wanghao666123/dummy_study/esp32-iot/firmware/examples/device-dashboard/screenshots/dashboard.webp

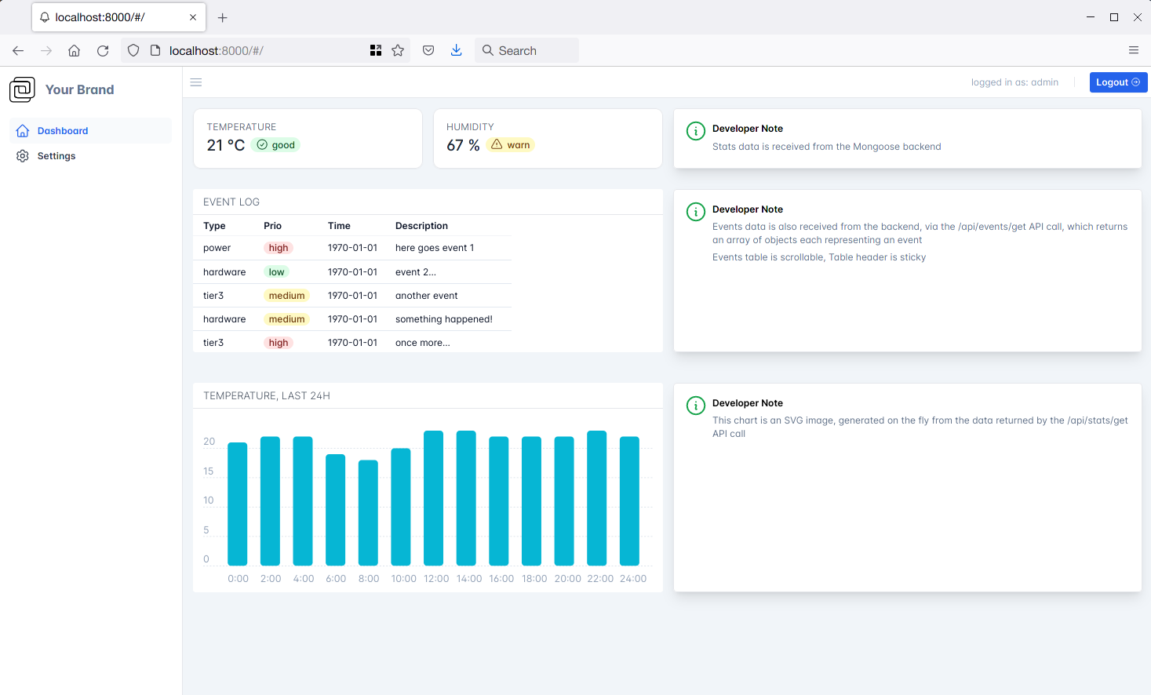
esp32-iot/firmware/examples/device-dashboard/screenshots/dashboard.webp
