wanghao666123/dummy_study/esp32-iot/firmware/examples/device-dashboard/screenshots/login.webp

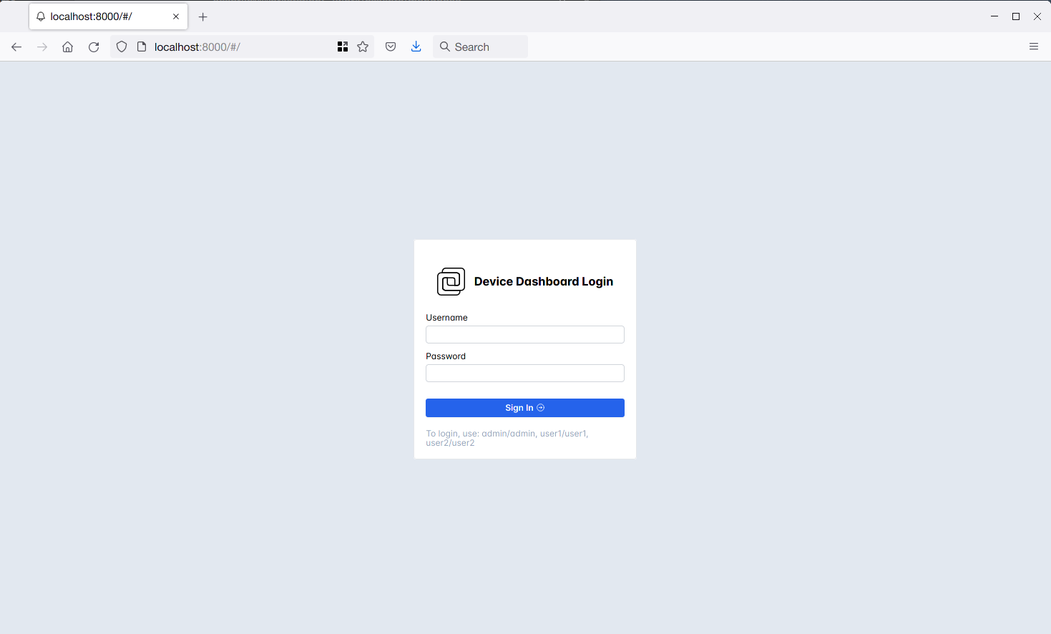
esp32-iot/firmware/examples/device-dashboard/screenshots/login.webp
