wanghao666123/dummy_study/esp32-iot/firmware/examples/uart-bridge/screenshots/dashboard.png

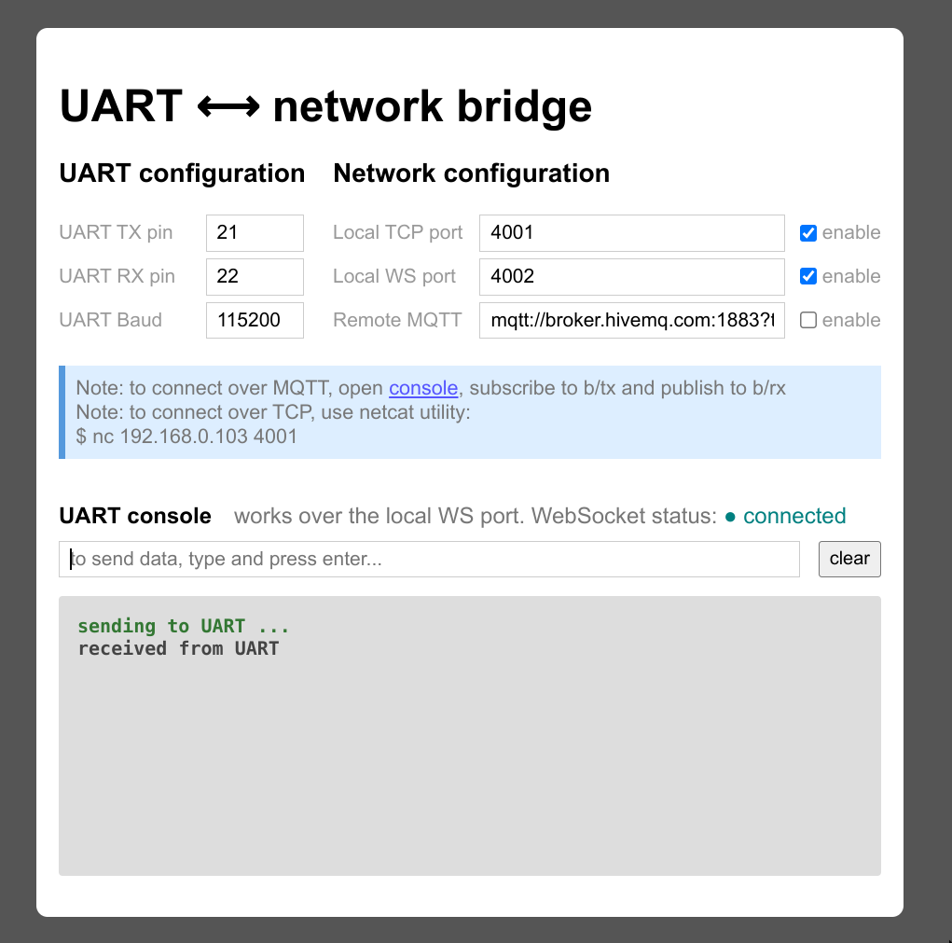
esp32-iot/firmware/examples/uart-bridge/screenshots/dashboard.png
