wanghao666123/dummy_study/esp32-iot/firmware/examples/video-stream/images/5.jpg

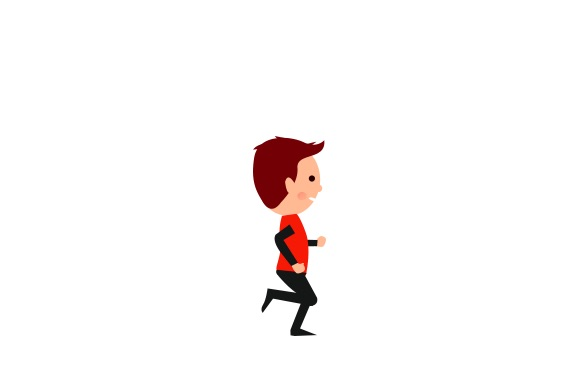
esp32-iot/firmware/examples/video-stream/images/5.jpg
