wanghao666123/dummy_study/esp32-iot/firmware/examples/webui-login/web_root/user.png

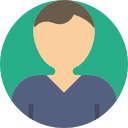
esp32-iot/firmware/examples/webui-login/web_root/user.png
