wanghao666123/dummy_study/harmonic_reducer/mini8_parameters.JPG

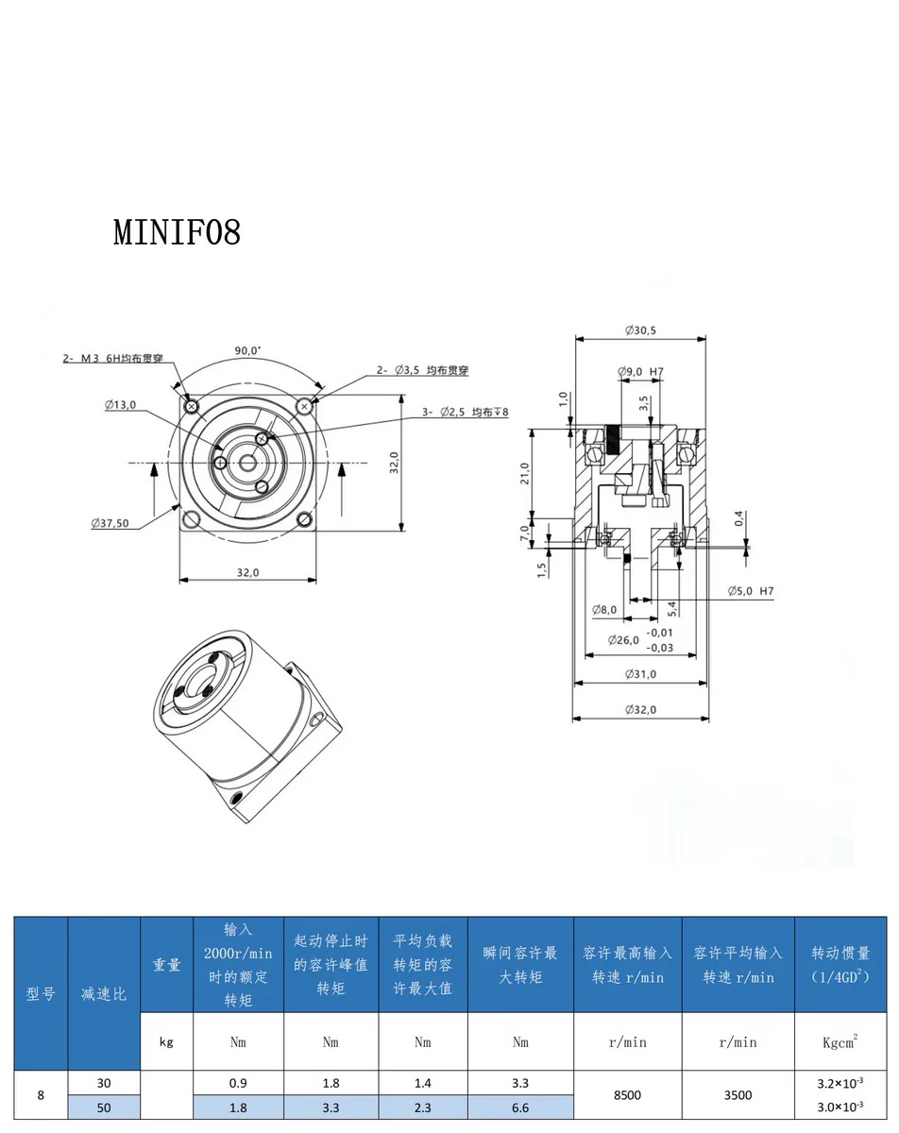
harmonic_reducer/mini8_parameters.JPG
