wanghao666123/dummy_study/harmonic_reducer/mini11_parameters.JPG

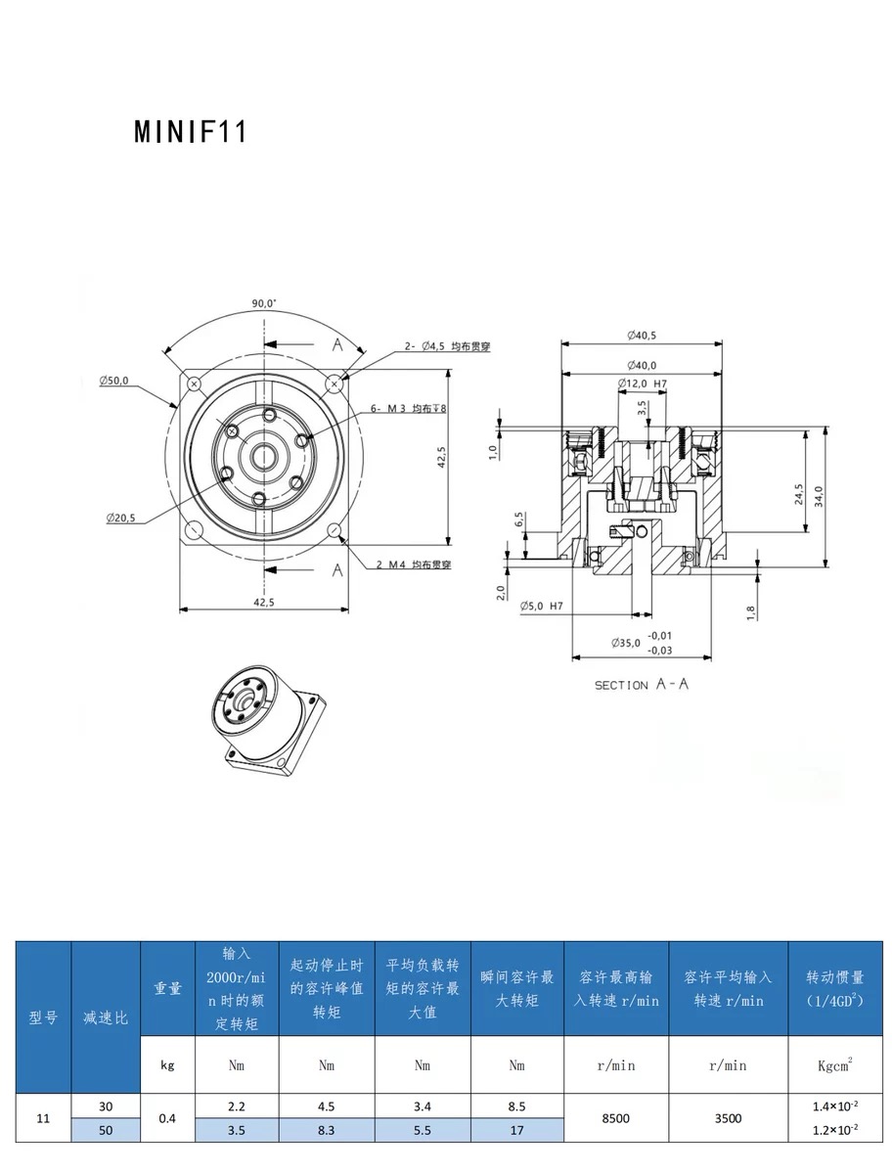
harmonic_reducer/mini11_parameters.JPG
