wanghao666123/dummy_study/ros2/dummy_ws/src/dummy-ros2_description/meshes/link2_1_1.stl

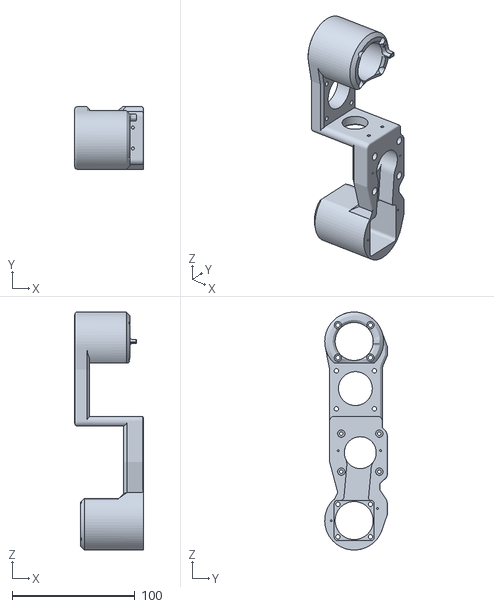
[picture p33: CAD file, 2024-07-29]
ros2/dummy_ws/src/dummy-ros2_description/meshes/link2_1_1.stl
55.8 x 51.0 x 194.0
