wanghao666123/dummy_study/ros2/dummy_ws/src/dummy-ros2_description/meshes/link3_1_1.stl

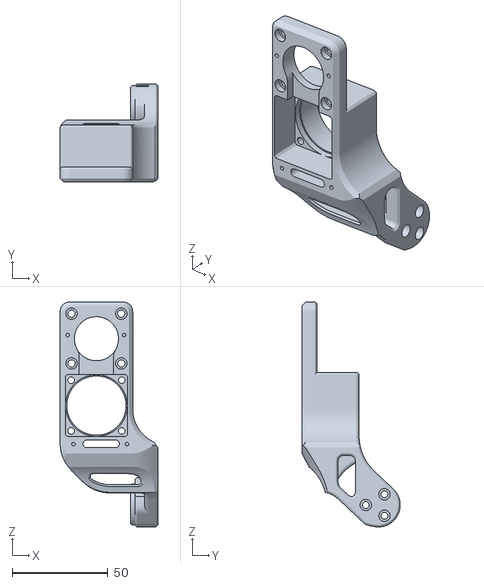
[picture p34: CAD file, 2024-07-29]
ros2/dummy_ws/src/dummy-ros2_description/meshes/link3_1_1.stl
51.1 x 51.5 x 117.7
