wanghao666123/dummy_study/ros2/dummy_ws/src/dummy-ros2_description/meshes/link5_1_1.stl

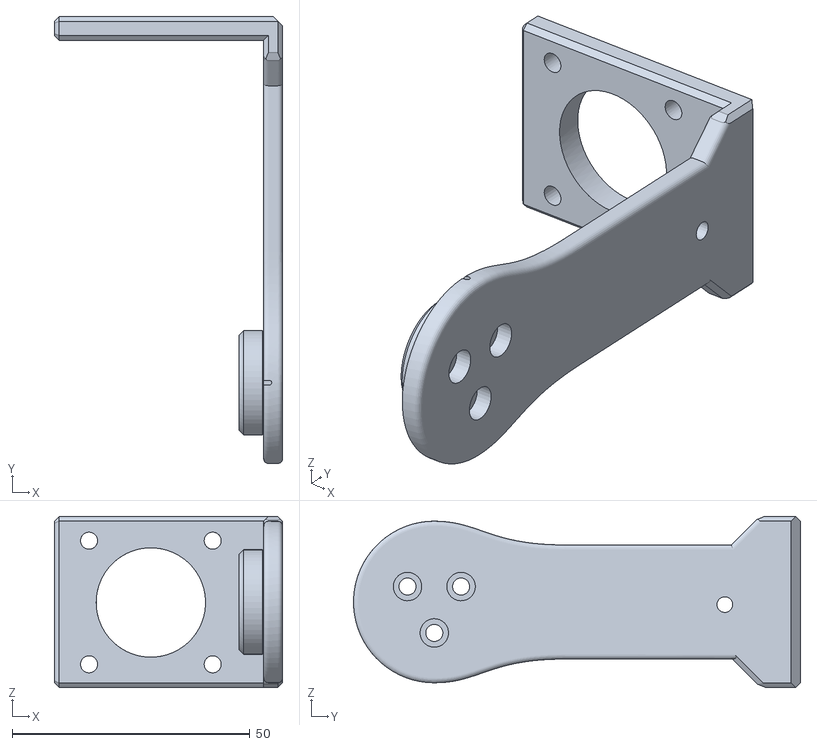
[picture p35: CAD file, 2024-07-29]
ros2/dummy_ws/src/dummy-ros2_description/meshes/link5_1_1.stl
48.0 x 94.0 x 36.0
