wanghao666123/dummy_study/3d-model/joint6.stl

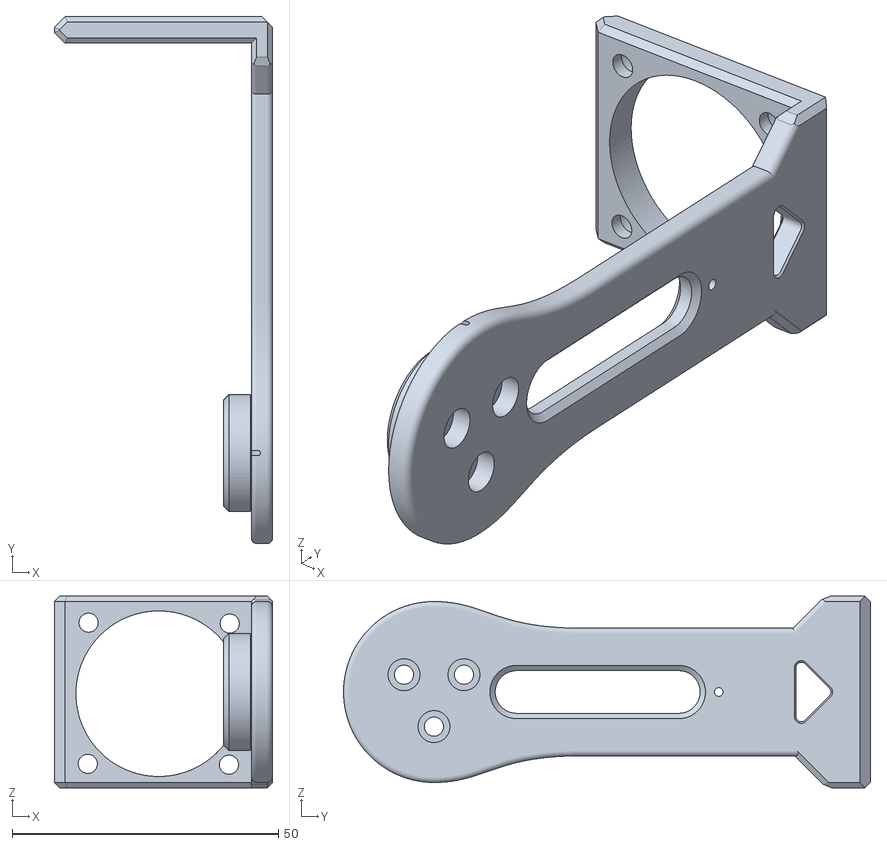
[picture p36: CAD file, 2023-11-14]
3d-model/joint6.stl
41.0 x 99.0 x 36.0
