wanghao666123/dummy_study/3d-model/latest/j4.stl

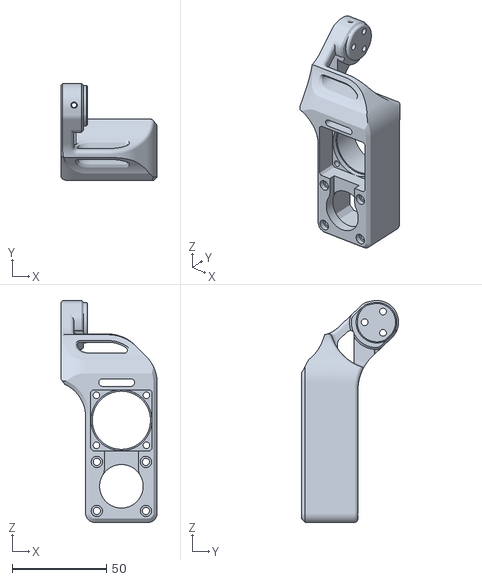
[picture p37: CAD file, 2023-12-19]
3d-model/latest/j4.stl
51.1 x 51.5 x 117.7
