wanghao666123/dummy_study/ros2/dummy_ws/src/dummy-ros2_description/meshes/base_link.stl

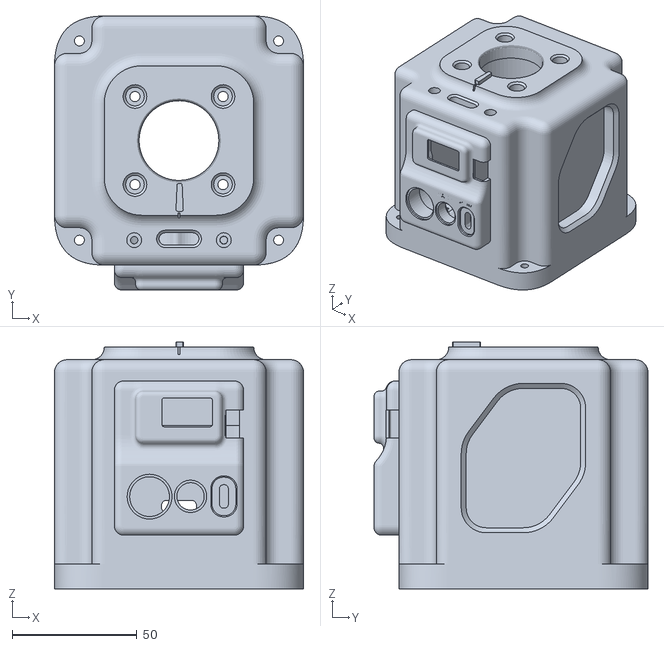
[picture p38: CAD file, 2024-07-29]
ros2/dummy_ws/src/dummy-ros2_description/meshes/base_link.stl
100.0 x 110.0 x 99.0
