wanghao666123/dummy_study/3d-model/joint23.stl

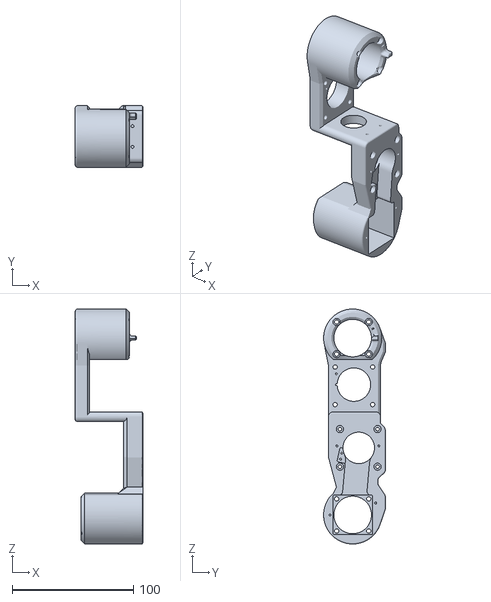
[picture p39: CAD file, 2023-11-14]
3d-model/joint23.stl
55.9 x 51.0 x 194.0
