wanghao666123/dummy_study/firmware/dummy-ref-core-fw/Robot/actuators/ctrl_step/ctrl_step.cpp

#include "ctrl_step.hpp"
#include "communication.hpp"


CtrlStepMotor::CtrlStepMotor(CAN_HandleTypeDef* _hcan, uint8_t _id, bool _inverse,
                             uint8_t _reduction, float _angleLimitMin, float _angleLimitMax) :
    nodeID(_id), hcan(_hcan), inverseDirection(_inverse), reduction(_reduction),
    angleLimitMin(_angleLimitMin), angleLimitMax(_angleLimitMax)
{
    txHeader =
        {
            .StdId = 0,
            .ExtId = 0,
            .IDE = CAN_ID_STD,
            .RTR = CAN_RTR_DATA,
            .DLC = 8,
            .TransmitGlobalTime = DISABLE
        };
}


void CtrlStepMotor::SetEnable(bool _enable)
{
    state = _enable ? FINISH : STOP;

    uint8_t mode = 0x01;
    txHeader.StdId = nodeID << 7 | mode;

    // Int to Bytes
    uint32_t val = _enable ? 1 : 0;
    auto* b = (unsigned char*) &val;
    for (int i = 0; i < 4; i++)
        canBuf[i] = *(b + i);

    CanSendMessage(get_can_ctx(hcan), canBuf, &txHeader);
}

void CtrlStepMotor::SetEnableTemp(bool _enable)
{
    uint8_t mode = 0x7d;
    txHeader.StdId = nodeID << 7 | mode;

    // Int to Bytes
    uint32_t val = _enable ? 1 : 0;
    auto* b = (unsigned char*) &val;
    for (int i = 0; i < 4; i++)
        canBuf[i] = *(b + i);

    CanSendMessage(get_can_ctx(hcan), canBuf, &txHeader);
}

void CtrlStepMotor::DoCalibration()
{
    uint8_t mode = 0x02;
    txHeader.StdId = nodeID << 7 | mode;

    CanSendMessage(get_can_ctx(hcan), canBuf, &txHeader);
}


void CtrlStepMotor::SetCurrentSetPoint(float _val)
{
    state = RUNNING;

    uint8_t mode = 0x03;
    txHeader.StdId = nodeID << 7 | mode;

    // Float to Bytes
    auto* b = (unsigned char*) &_val;
    for (int i = 0; i < 4; i++)
        canBuf[i] = *(b + i);

    CanSendMessage(get_can_ctx(hcan), canBuf, &txHeader);
}


void CtrlStepMotor::SetVelocitySetPoint(float _val)
{
    state = RUNNING;

    uint8_t mode = 0x04;
    txHeader.StdId = nodeID << 7 | mode;

    // Float to Bytes
    auto* b = (unsigned char*) &_val;
    for (int i = 0; i < 4; i++)
        canBuf[i] = *(b + i);

    CanSendMessage(get_can_ctx(hcan), canBuf, &txHeader);
}


void CtrlStepMotor::SetPositionSetPoint(float _val)
{
    uint8_t mode = 0x05;
    txHeader.StdId = nodeID << 7 | mode;

    // Float to Bytes
    auto* b = (unsigned char*) &_val;
    for (int i = 0; i < 4; i++)
        canBuf[i] = *(b + i);
    canBuf[4] = 1; // Need ACK

    CanSendMessage(get_can_ctx(hcan), canBuf, &txHeader);
}


void CtrlStepMotor::SetPositionWithVelocityLimit(float _pos, float _vel)
{
    uint8_t mode = 0x07;
    txHeader.StdId = nodeID << 7 | mode;

    // Float to Bytes
    auto* b = (unsigned char*) &_pos;
    for (int i = 0; i < 4; i++)
        canBuf[i] = *(b + i);
    b = (unsigned char*) &_vel;
    for (int i = 4; i < 8; i++)
        canBuf[i] = *(b + i - 4);

    CanSendMessage(get_can_ctx(hcan), canBuf, &txHeader);
}


void CtrlStepMotor::SetNodeID(uint32_t _id)
{
    uint8_t mode = 0x11;
    txHeader.StdId = nodeID << 7 | mode;

    // Int to Bytes
    auto* b = (unsigned char*) &_id;
    for (int i = 0; i < 4; i++)
        canBuf[i] = *(b + i);
    canBuf[4] = 1; // Need save to EEPROM or not

    CanSendMessage(get_can_ctx(hcan), canBuf, &txHeader);
}


void CtrlStepMotor::SetCurrentLimit(float _val)
{
    uint8_t mode = 0x12;
    txHeader.StdId = nodeID << 7 | mode;

    // Float to Bytes
    auto* b = (unsigned char*) &_val;
    for (int i = 0; i < 4; i++)
        canBuf[i] = *(b + i);
    canBuf[4] = 1; // Need save to EEPROM or not

    CanSendMessage(get_can_ctx(hcan), canBuf, &txHeader);
}


void CtrlStepMotor::SetVelocityLimit(float _val)
{
    uint8_t mode = 0x13;
    txHeader.StdId = nodeID << 7 | mode;

    // Float to Bytes
    auto* b = (unsigned char*) &_val;
    for (int i = 0; i < 4; i++)
        canBuf[i] = *(b + i);
    canBuf[4] = 1; // Need save to EEPROM or not

    CanSendMessage(get_can_ctx(hcan), canBuf, &txHeader);
}


void CtrlStepMotor::SetAcceleration(float _val)
{
    uint8_t mode = 0x14;
    txHeader.StdId = nodeID << 7 | mode;

    // Float to Bytes
    auto* b = (unsigned char*) &_val;
    for (int i = 0; i < 4; i++)
        canBuf[i] = *(b + i);
    canBuf[4] = 0; // Need save to EEPROM or not

    CanSendMessage(get_can_ctx(hcan), canBuf, &txHeader);
}


void CtrlStepMotor::ApplyPositionAsHome()
{
    uint8_t mode = 0x15;
    txHeader.StdId = nodeID << 7 | mode;

    CanSendMessage(get_can_ctx(hcan), canBuf, &txHeader);
}


void CtrlStepMotor::SetEnableOnBoot(bool _enable)
{
    uint8_t mode = 0x16;
    txHeader.StdId = nodeID << 7 | mode;

    // Int to Bytes
    uint32_t val = _enable ? 1 : 0;
    auto* b = (unsigned char*) &val;
    for (int i = 0; i < 4; i++)
        canBuf[i] = *(b + i);
    canBuf[4] = 1; // Need save to EEPROM or not

    CanSendMessage(get_can_ctx(hcan), canBuf, &txHeader);
}


void CtrlStepMotor::SetEnableStallProtect(bool _enable)
{
    uint8_t mode = 0x1B;
    txHeader.StdId = nodeID << 7 | mode;

    uint32_t val = _enable ? 1 : 0;
    auto* b = (unsigned char*) &val;
    for (int i = 0; i < 4; i++)
        canBuf[i] = *(b + i);
    canBuf[4] = 1; // Need save to EEPROM or not

    CanSendMessage(get_can_ctx(hcan), canBuf, &txHeader);
}


void CtrlStepMotor::Reboot()
{
    uint8_t mode = 0x7f;
    txHeader.StdId = nodeID << 7 | mode;

    CanSendMessage(get_can_ctx(hcan), canBuf, &txHeader);
}

uint32_t CtrlStepMotor::GetTemp()
{
    uint8_t mode = 0x25;
    txHeader.StdId = nodeID << 7 | mode;

    CanSendMessage(get_can_ctx(hcan), canBuf, &txHeader);
    return temperature;
}

void CtrlStepMotor::EraseConfigs()
{
    uint8_t mode = 0x7e;
    txHeader.StdId = nodeID << 7 | mode;

    CanSendMessage(get_can_ctx(hcan), canBuf, &txHeader);
}


void CtrlStepMotor::SetAngle(float _angle)
{
    _angle = inverseDirection ? -_angle : _angle;
    float stepMotorCnt = _angle / 360.0f * (float) reduction;
    SetPositionSetPoint(stepMotorCnt);
}


void CtrlStepMotor::SetAngleWithVelocityLimit(float _angle, float _vel)
{
    _angle = inverseDirection ? -_angle : _angle;
    //!关节的目标转动角度对应的步近电机的步进计数，相当于关节映射到电机需要转多少数
    float stepMotorCnt = _angle / 360.0f * (float) reduction;
    //!通过can发送电机需要转多少数和速度限制
    SetPositionWithVelocityLimit(stepMotorCnt, _vel);
}


void CtrlStepMotor::UpdateAngle()
{
    uint8_t mode = 0x23;
    txHeader.StdId = nodeID << 7 | mode;

    CanSendMessage(get_can_ctx(hcan), canBuf, &txHeader);
}


void CtrlStepMotor::UpdateAngleCallback(float _pos, bool _isFinished)
{
    state = _isFinished ? FINISH : RUNNING;
    //!这里解算成关节的角度
    float tmp = _pos / (float) reduction * 360;
    angle = inverseDirection ? -tmp : tmp;
}


void CtrlStepMotor::SetDceKp(int32_t _val)
{
    uint8_t mode = 0x17;
    txHeader.StdId = nodeID << 7 | mode;

    auto* b = (unsigned char*) &_val;
    for (int i = 0; i < 4; i++)
        canBuf[i] = *(b + i);
    canBuf[4] = 1; // Need save to EEPROM or not

    CanSendMessage(get_can_ctx(hcan), canBuf, &txHeader);
}


void CtrlStepMotor::SetDceKv(int32_t _val)
{
    uint8_t mode = 0x18;
    txHeader.StdId = nodeID << 7 | mode;

    auto* b = (unsigned char*) &_val;
    for (int i = 0; i < 4; i++)
        canBuf[i] = *(b + i);
    canBuf[4] = 1; // Need save to EEPROM or not

    CanSendMessage(get_can_ctx(hcan), canBuf, &txHeader);
}


void CtrlStepMotor::SetDceKi(int32_t _val)
{
    uint8_t mode = 0x19;
    txHeader.StdId = nodeID << 7 | mode;

    auto* b = (unsigned char*) &_val;
    for (int i = 0; i < 4; i++)
        canBuf[i] = *(b + i);
    canBuf[4] = 1; // Need save to EEPROM or not

    CanSendMessage(get_can_ctx(hcan), canBuf, &txHeader);
}


void CtrlStepMotor::SetDceKd(int32_t _val)
{
    uint8_t mode = 0x1A;
    txHeader.StdId = nodeID << 7 | mode;

    auto* b = (unsigned char*) &_val;
    for (int i = 0; i < 4; i++)
        canBuf[i] = *(b + i);
    canBuf[4] = 1; // Need save to EEPROM or not

    CanSendMessage(get_can_ctx(hcan), canBuf, &txHeader);
}
