wanghao666123/dummy_study/ros2/dummy_ws/src/dummy_moveit_config/config/initial_positions.yaml

# Default initial positions for dummy-ros2's ros2_control fake system

initial_positions:
  Joint1: 0
  Joint2: 0
  Joint3: 0
  Joint4: 0
  Joint5: 0
  Joint6: 0
