wanghao666123/dummy_study/firmware/dummy-ref-core-fw/Bsp/imu/MPU6050.cpp

// I2Cdev library collection - MPU6050 I2C device class
// Based on InvenSense MPU-6050 register map document rev. 2.0, 5/19/2011 (RM-MPU-6000A-00)
// 8/24/2011 by Jeff Rowberg <jeff@rowberg.net>
// Updates should (hopefully) always be available at https://github.com/jrowberg/i2cdevlib
//
// Changelog:
//     ... - ongoing debug release

// NOTE: THIS IS ONLY A PARIAL RELEASE. THIS DEVICE CLASS IS CURRENTLY UNDERGOING ACTIVE
// DEVELOPMENT AND IS STILL MISSING SOME IMPORTANT FEATURES. PLEASE KEEP THIS IN MIND IF
// YOU DECIDE TO USE THIS PARTICULAR CODE FOR ANYTHING.

/* ============================================
I2Cdev device library code is placed under the MIT license
Copyright (c) 2012 Jeff Rowberg

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
THE SOFTWARE IS PROVIDED "AS IS", WITHOUT WARRANTY OF ANY KIND, EXPRESS OR
IMPLIED, INCLUDING BUT NOT LIMITED TO THE WARRANTIES OF MERCHANTABILITY,
FITNESS FOR A PARTICULAR PURPOSE AND NONINFRINGEMENT. IN NO EVENT SHALL THE
AUTHORS OR COPYRIGHT HOLDERS BE LIABLE FOR ANY CLAIM, DAMAGES OR OTHER
LIABILITY, WHETHER IN AN ACTION OF CONTRACT, TORT OR OTHERWISE, ARISING FROM,
OUT OF OR IN CONNECTION WITH THE SOFTWARE OR THE USE OR OTHER DEALINGS IN
THE SOFTWARE.
===============================================
*/

#include "mpu6050.hpp"

#define pgm_read_byte(addr)   (*(const unsigned char *)(addr))

/** Specific address constructor.
 * @param address I2C address, uses default I2C address if none is specified
 * @see MPU6050_DEFAULT_ADDRESS
 * @see MPU6050_ADDRESS_AD0_LOW
 * @see MPU6050_ADDRESS_AD0_HIGH
 */
MPU6050::MPU6050(I2C_HandleTypeDef *_hi2c, uint8_t address) : hi2c(_hi2c), devAddr(address)
{
    I2Cdev_init(hi2c);

    InitFilter();
}

/** Power on and prepare for general usage.
 * This will activate the device and take it out of sleep mode (which must be done
 * after start-up). This function also sets both the accelerometer and the gyroscope
 * to their most sensitive settings, namely +/- 2g and +/- 250 degrees/sec, and sets
 * the clock source to use the X Gyro for reference, which is slightly better than
 * the default internal clock source.
 */
void MPU6050::Init()
{
    setClockSource(MPU6050_CLOCK_PLL_XGYRO);
    setFullScaleGyroRange(MPU6050_GYRO_FS_250);
    setFullScaleAccelRange(MPU6050_ACCEL_FS_2);
    setDLPFMode(MPU6050_DLPF_BW_98);
    setSleepEnabled(false); // thanks to Jack Elston for pointing this one out!
}

/** Verify the I2C connection.
 * Make sure the device is connected and responds as expected.
 * @return True if connection is valid, false otherwise
 */
bool MPU6050::testConnection()
{
    return getDeviceID() == 0x34;
}

// AUX_VDDIO register (InvenSense demo code calls this RA_*G_OFFS_TC)

/** Get the auxiliary I2C supply voltage level.
 * When set to 1, the auxiliary I2C bus high logic level is VDD. When cleared to
 * 0, the auxiliary I2C bus high logic level is VLOGIC. This does not apply to
 * the MPU-6000, which does not have a VLOGIC pin.
 * @return I2C supply voltage level (0=VLOGIC, 1=VDD)
 */
uint8_t MPU6050::getAuxVDDIOLevel()
{
    I2Cdev_readBit(devAddr, MPU6050_RA_YG_OFFS_TC, MPU6050_TC_PWR_MODE_BIT, buffer);
    return buffer[0];
}

/** Set the auxiliary I2C supply voltage level.
 * When set to 1, the auxiliary I2C bus high logic level is VDD. When cleared to
 * 0, the auxiliary I2C bus high logic level is VLOGIC. This does not apply to
 * the MPU-6000, which does not have a VLOGIC pin.
 * @param level I2C supply voltage level (0=VLOGIC, 1=VDD)
 */
void MPU6050::setAuxVDDIOLevel(uint8_t level)
{
    I2Cdev_writeBit(devAddr, MPU6050_RA_YG_OFFS_TC, MPU6050_TC_PWR_MODE_BIT, level);
}

// SMPLRT_DIV register

/** Get gyroscope output rate divider.
 * The sensor register output, FIFO output, DMP sampling, Motion detection, Zero
 * Motion detection, and Free Fall detection are all based on the Sample Rate.
 * The Sample Rate is generated by dividing the gyroscope output rate by
 * SMPLRT_DIV:
 *
 * Sample Rate = Gyroscope Output Rate / (1 + SMPLRT_DIV)
 *
 * where Gyroscope Output Rate = 8kHz when the DLPF is disabled (DLPF_CFG = 0 or
 * 7), and 1kHz when the DLPF is enabled (see Register 26).
 *
 * Note: The accelerometer output rate is 1kHz. This means that for a Sample
 * Rate greater than 1kHz, the same accelerometer sample may be output to the
 * FIFO, DMP, and sensor registers more than once.
 *
 * For a diagram of the gyroscope and accelerometer signal paths, see Section 8
 * of the MPU-6000/MPU-6050 Product Specification document.
 *
 * @return Current sample rate
 * @see MPU6050_RA_SMPLRT_DIV
 */
uint8_t MPU6050::getRate()
{
    I2Cdev_readByte(devAddr, MPU6050_RA_SMPLRT_DIV, buffer);
    return buffer[0];
}

/** Set gyroscope sample rate divider.
 * @param rate New sample rate divider
 * @see getRate()
 * @see MPU6050_RA_SMPLRT_DIV
 */
void MPU6050::setRate(uint8_t rate)
{
    I2Cdev_writeByte(devAddr, MPU6050_RA_SMPLRT_DIV, rate);
}

// CONFIG register

/** Get external FSYNC configuration.
 * Configures the external Frame Synchronization (FSYNC) pin sampling. An
 * external signal connected to the FSYNC pin can be sampled by configuring
 * EXT_SYNC_SET. Signal changes to the FSYNC pin are latched so that short
 * strobes may be captured. The latched FSYNC signal will be sampled at the
 * Sampling Rate, as defined in register 25. After sampling, the latch will
 * reset to the current FSYNC signal state.
 *
 * The sampled value will be reported in place of the least significant bit in
 * a sensor data register determined by the value of EXT_SYNC_SET according to
 * the following table.
 *
 * <pre>
 * EXT_SYNC_SET | FSYNC Bit Location
 * -------------+-------------------
 * 0            | Input disabled
 * 1            | TEMP_OUT_L[0]
 * 2            | GYRO_XOUT_L[0]
 * 3            | GYRO_YOUT_L[0]
 * 4            | GYRO_ZOUT_L[0]
 * 5            | ACCEL_XOUT_L[0]
 * 6            | ACCEL_YOUT_L[0]
 * 7            | ACCEL_ZOUT_L[0]
 * </pre>
 *
 * @return FSYNC configuration value
 */
uint8_t MPU6050::getExternalFrameSync()
{
    I2Cdev_readBits(devAddr, MPU6050_RA_CONFIG, MPU6050_CFG_EXT_SYNC_SET_BIT, MPU6050_CFG_EXT_SYNC_SET_LENGTH, buffer);
    return buffer[0];
}

/** Set external FSYNC configuration.
 * @see getExternalFrameSync()
 * @see MPU6050_RA_CONFIG
 * @param sync New FSYNC configuration value
 */
void MPU6050::setExternalFrameSync(uint8_t sync)
{
    I2Cdev_writeBits(devAddr, MPU6050_RA_CONFIG, MPU6050_CFG_EXT_SYNC_SET_BIT, MPU6050_CFG_EXT_SYNC_SET_LENGTH, sync);
}

/** Get digital low-pass filter configuration.
 * The DLPF_CFG parameter sets the digital low pass filter configuration. It
 * also determines the internal sampling rate used by the device as shown in
 * the table below.
 *
 * Note: The accelerometer output rate is 1kHz. This means that for a Sample
 * Rate greater than 1kHz, the same accelerometer sample may be output to the
 * FIFO, DMP, and sensor registers more than once.
 *
 * <pre>
 *          |   ACCELEROMETER    |           GYROSCOPE
 * DLPF_CFG | Bandwidth | Delay  | Bandwidth | Delay  | Sample Rate
 * ---------+-----------+--------+-----------+--------+-------------
 * 0        | 260Hz     | 0ms    | 256Hz     | 0.98ms | 8kHz
 * 1        | 184Hz     | 2.0ms  | 188Hz     | 1.9ms  | 1kHz
 * 2        | 94Hz      | 3.0ms  | 98Hz      | 2.8ms  | 1kHz
 * 3        | 44Hz      | 4.9ms  | 42Hz      | 4.8ms  | 1kHz
 * 4        | 21Hz      | 8.5ms  | 20Hz      | 8.3ms  | 1kHz
 * 5        | 10Hz      | 13.8ms | 10Hz      | 13.4ms | 1kHz
 * 6        | 5Hz       | 19.0ms | 5Hz       | 18.6ms | 1kHz
 * 7        |   -- Reserved --   |   -- Reserved --   | Reserved
 * </pre>
 *
 * @return DLFP configuration
 * @see MPU6050_RA_CONFIG
 * @see MPU6050_CFG_DLPF_CFG_BIT
 * @see MPU6050_CFG_DLPF_CFG_LENGTH
 */
uint8_t MPU6050::getDLPFMode()
{
    I2Cdev_readBits(devAddr, MPU6050_RA_CONFIG, MPU6050_CFG_DLPF_CFG_BIT, MPU6050_CFG_DLPF_CFG_LENGTH, buffer);
    return buffer[0];
}

/** Set digital low-pass filter configuration.
 * @param mode New DLFP configuration setting
 * @see getDLPFBandwidth()
 * @see MPU6050_DLPF_BW_256
 * @see MPU6050_RA_CONFIG
 * @see MPU6050_CFG_DLPF_CFG_BIT
 * @see MPU6050_CFG_DLPF_CFG_LENGTH
 */
void MPU6050::setDLPFMode(uint8_t mode)
{
    I2Cdev_writeBits(devAddr, MPU6050_RA_CONFIG, MPU6050_CFG_DLPF_CFG_BIT, MPU6050_CFG_DLPF_CFG_LENGTH, mode);
}

// GYRO_CONFIG register

/** Get full-scale gyroscope range.
 * The FS_SEL parameter allows setting the full-scale range of the gyro sensors,
 * as described in the table below.
 *
 * <pre>
 * 0 = +/- 250 degrees/sec
 * 1 = +/- 500 degrees/sec
 * 2 = +/- 1000 degrees/sec
 * 3 = +/- 2000 degrees/sec
 * </pre>
 *
 * @return Current full-scale gyroscope range setting
 * @see MPU6050_GYRO_FS_250
 * @see MPU6050_RA_GYRO_CONFIG
 * @see MPU6050_GCONFIG_FS_SEL_BIT
 * @see MPU6050_GCONFIG_FS_SEL_LENGTH
 */
uint8_t MPU6050::getFullScaleGyroRange()
{
    I2Cdev_readBits(devAddr, MPU6050_RA_GYRO_CONFIG, MPU6050_GCONFIG_FS_SEL_BIT, MPU6050_GCONFIG_FS_SEL_LENGTH,
                    buffer);
    return buffer[0];
}

/** Set full-scale gyroscope range.
 * @param range New full-scale gyroscope range value
 * @see getFullScaleRange()
 * @see MPU6050_GYRO_FS_250
 * @see MPU6050_RA_GYRO_CONFIG
 * @see MPU6050_GCONFIG_FS_SEL_BIT
 * @see MPU6050_GCONFIG_FS_SEL_LENGTH
 */
void MPU6050::setFullScaleGyroRange(uint8_t range)
{
    I2Cdev_writeBits(devAddr, MPU6050_RA_GYRO_CONFIG, MPU6050_GCONFIG_FS_SEL_BIT, MPU6050_GCONFIG_FS_SEL_LENGTH,
                     range);

    switch (range)
    {
        case MPU6050_GYRO_FS_250:
            gyroRangeScale = 32768 / 250.0;
            break;
        case MPU6050_GYRO_FS_500:
            gyroRangeScale = 32768 / 500.0;
            break;
        case MPU6050_GYRO_FS_1000:
            gyroRangeScale = 32768 / 1000.0;
            break;
        case MPU6050_GYRO_FS_2000:
            gyroRangeScale = 32768 / 2000.0;
            break;
        default:
            break;
    }
}

// SELF TEST FACTORY TRIM VALUES

/** Get self-test factory trim value for accelerometer X axis.
 * @return factory trim value
 * @see MPU6050_RA_SELF_TEST_X
 */
uint8_t MPU6050::getAccelXSelfTestFactoryTrim()
{
    I2Cdev_readByte(devAddr, MPU6050_RA_SELF_TEST_X, &buffer[0]);
    I2Cdev_readByte(devAddr, MPU6050_RA_SELF_TEST_A, &buffer[1]);
    return (buffer[0] >> 3) | ((buffer[1] >> 4) & 0x03);
}

/** Get self-test factory trim value for accelerometer Y axis.
 * @return factory trim value
 * @see MPU6050_RA_SELF_TEST_Y
 */
uint8_t MPU6050::getAccelYSelfTestFactoryTrim()
{
    I2Cdev_readByte(devAddr, MPU6050_RA_SELF_TEST_Y, &buffer[0]);
    I2Cdev_readByte(devAddr, MPU6050_RA_SELF_TEST_A, &buffer[1]);
    return (buffer[0] >> 3) | ((buffer[1] >> 2) & 0x03);
}

/** Get self-test factory trim value for accelerometer Z axis.
 * @return factory trim value
 * @see MPU6050_RA_SELF_TEST_Z
 */
uint8_t MPU6050::getAccelZSelfTestFactoryTrim()
{
    I2Cdev_readBytes(devAddr, MPU6050_RA_SELF_TEST_Z, 2, buffer);
    return (buffer[0] >> 3) | (buffer[1] & 0x03);
}

/** Get self-test factory trim value for gyro X axis.
 * @return factory trim value
 * @see MPU6050_RA_SELF_TEST_X
 */
uint8_t MPU6050::getGyroXSelfTestFactoryTrim()
{
    I2Cdev_readByte(devAddr, MPU6050_RA_SELF_TEST_X, buffer);
    return (buffer[0] & 0x1F);
}

/** Get self-test factory trim value for gyro Y axis.
 * @return factory trim value
 * @see MPU6050_RA_SELF_TEST_Y
 */
uint8_t MPU6050::getGyroYSelfTestFactoryTrim()
{
    I2Cdev_readByte(devAddr, MPU6050_RA_SELF_TEST_Y, buffer);
    return (buffer[0] & 0x1F);
}

/** Get self-test factory trim value for gyro Z axis.
 * @return factory trim value
 * @see MPU6050_RA_SELF_TEST_Z
 */
uint8_t MPU6050::getGyroZSelfTestFactoryTrim()
{
    I2Cdev_readByte(devAddr, MPU6050_RA_SELF_TEST_Z, buffer);
    return (buffer[0] & 0x1F);
}

// ACCEL_CONFIG register

/** Get self-test enabled setting for accelerometer X axis.
 * @return Self-test enabled value
 * @see MPU6050_RA_ACCEL_CONFIG
 */
bool MPU6050::getAccelXSelfTest()
{
    I2Cdev_readBit(devAddr, MPU6050_RA_ACCEL_CONFIG, MPU6050_ACONFIG_XA_ST_BIT, buffer);
    return buffer[0];
}

/** Get self-test enabled setting for accelerometer X axis.
 * @param enabled Self-test enabled value
 * @see MPU6050_RA_ACCEL_CONFIG
 */
void MPU6050::setAccelXSelfTest(bool enabled)
{
    I2Cdev_writeBit(devAddr, MPU6050_RA_ACCEL_CONFIG, MPU6050_ACONFIG_XA_ST_BIT, enabled);
}

/** Get self-test enabled value for accelerometer Y axis.
 * @return Self-test enabled value
 * @see MPU6050_RA_ACCEL_CONFIG
 */
bool MPU6050::getAccelYSelfTest()
{
    I2Cdev_readBit(devAddr, MPU6050_RA_ACCEL_CONFIG, MPU6050_ACONFIG_YA_ST_BIT, buffer);
    return buffer[0];
}

/** Get self-test enabled value for accelerometer Y axis.
 * @param enabled Self-test enabled value
 * @see MPU6050_RA_ACCEL_CONFIG
 */
void MPU6050::setAccelYSelfTest(bool enabled)
{
    I2Cdev_writeBit(devAddr, MPU6050_RA_ACCEL_CONFIG, MPU6050_ACONFIG_YA_ST_BIT, enabled);
}

/** Get self-test enabled value for accelerometer Z axis.
 * @return Self-test enabled value
 * @see MPU6050_RA_ACCEL_CONFIG
 */
bool MPU6050::getAccelZSelfTest()
{
    I2Cdev_readBit(devAddr, MPU6050_RA_ACCEL_CONFIG, MPU6050_ACONFIG_ZA_ST_BIT, buffer);
    return buffer[0];
}

/** Set self-test enabled value for accelerometer Z axis.
 * @param enabled Self-test enabled value
 * @see MPU6050_RA_ACCEL_CONFIG
 */
void MPU6050::setAccelZSelfTest(bool enabled)
{
    I2Cdev_writeBit(devAddr, MPU6050_RA_ACCEL_CONFIG, MPU6050_ACONFIG_ZA_ST_BIT, enabled);
}

/** Get full-scale accelerometer range.
 * The FS_SEL parameter allows setting the full-scale range of the accelerometer
 * sensors, as described in the table below.
 *
 * <pre>
 * 0 = +/- 2g
 * 1 = +/- 4g
 * 2 = +/- 8g
 * 3 = +/- 16g
 * </pre>
 *
 * @return Current full-scale accelerometer range setting
 * @see MPU6050_ACCEL_FS_2
 * @see MPU6050_RA_ACCEL_CONFIG
 * @see MPU6050_ACONFIG_AFS_SEL_BIT
 * @see MPU6050_ACONFIG_AFS_SEL_LENGTH
 */
uint8_t MPU6050::getFullScaleAccelRange()
{
    I2Cdev_readBits(devAddr, MPU6050_RA_ACCEL_CONFIG, MPU6050_ACONFIG_AFS_SEL_BIT, MPU6050_ACONFIG_AFS_SEL_LENGTH,
                    buffer);
    return buffer[0];
}

/** Set full-scale accelerometer range.
 * @param range New full-scale accelerometer range setting
 * @see getFullScaleAccelRange()
 */
void MPU6050::setFullScaleAccelRange(uint8_t range)
{
    I2Cdev_writeBits(devAddr, MPU6050_RA_ACCEL_CONFIG, MPU6050_ACONFIG_AFS_SEL_BIT, MPU6050_ACONFIG_AFS_SEL_LENGTH,
                     range);

    switch (range)
    {
        case MPU6050_ACCEL_FS_2:
            accRangeScale = 32768 / 2.0;
            break;
        case MPU6050_ACCEL_FS_4:
            accRangeScale = 32768 / 4.0;
            break;
        case MPU6050_ACCEL_FS_8:
            accRangeScale = 32768 / 8.0;
            break;
        case MPU6050_ACCEL_FS_16:
            accRangeScale = 32768 / 16.0;
            break;
        default:
            break;
    }
}

/** Get the high-pass filter configuration.
 * The DHPF is a filter module in the path leading to motion detectors (Free
 * Fall, Motion threshold, and Zero Motion). The high pass filter output is not
 * available to the data registers (see Figure in Section 8 of the MPU-6000/
 * MPU-6050 Product Specification document).
 *
 * The high pass filter has three modes:
 *
 * <pre>
 *    Reset: The filter output settles to zero within one sample. This
 *           effectively disables the high pass filter. This mode may be toggled
 *           to quickly settle the filter.
 *
 *    On:    The high pass filter will pass signals above the cut off frequency.
 *
 *    Hold:  When triggered, the filter holds the present sample. The filter
 *           output will be the difference between the input sample and the held
 *           sample.
 * </pre>
 *
 * <pre>
 * ACCEL_HPF | Filter Mode | Cut-off Frequency
 * ----------+-------------+------------------
 * 0         | Reset       | None
 * 1         | On          | 5Hz
 * 2         | On          | 2.5Hz
 * 3         | On          | 1.25Hz
 * 4         | On          | 0.63Hz
 * 7         | Hold        | None
 * </pre>
 *
 * @return Current high-pass filter configuration
 * @see MPU6050_DHPF_RESET
 * @see MPU6050_RA_ACCEL_CONFIG
 */
uint8_t MPU6050::getDHPFMode()
{
    I2Cdev_readBits(devAddr, MPU6050_RA_ACCEL_CONFIG, MPU6050_ACONFIG_ACCEL_HPF_BIT, MPU6050_ACONFIG_ACCEL_HPF_LENGTH,
                    buffer);
    return buffer[0];
}

/** Set the high-pass filter configuration.
 * @param bandwidth New high-pass filter configuration
 * @see setDHPFMode()
 * @see MPU6050_DHPF_RESET
 * @see MPU6050_RA_ACCEL_CONFIG
 */
void MPU6050::setDHPFMode(uint8_t bandwidth)
{
    I2Cdev_writeBits(devAddr, MPU6050_RA_ACCEL_CONFIG, MPU6050_ACONFIG_ACCEL_HPF_BIT, MPU6050_ACONFIG_ACCEL_HPF_LENGTH,
                     bandwidth);
}

// FF_THR register

/** Get free-fall event acceleration threshold.
 * This register configures the detection threshold for Free Fall event
 * detection. The unit of FF_THR is 1LSB = 2mg. Free Fall is detected when the
 * absolute value of the accelerometer measurements for the three axes are each
 * less than the detection threshold. This condition increments the Free Fall
 * duration counter (Register 30). The Free Fall interrupt is triggered when the
 * Free Fall duration counter reaches the time specified in FF_DUR.
 *
 * For more details on the Free Fall detection interrupt, see Section 8.2 of the
 * MPU-6000/MPU-6050 Product Specification document as well as Registers 56 and
 * 58 of this document.
 *
 * @return Current free-fall acceleration threshold value (LSB = 2mg)
 * @see MPU6050_RA_FF_THR
 */
uint8_t MPU6050::getFreefallDetectionThreshold()
{
    I2Cdev_readByte(devAddr, MPU6050_RA_FF_THR, buffer);
    return buffer[0];
}

/** Get free-fall event acceleration threshold.
 * @param threshold New free-fall acceleration threshold value (LSB = 2mg)
 * @see getFreefallDetectionThreshold()
 * @see MPU6050_RA_FF_THR
 */
void MPU6050::setFreefallDetectionThreshold(uint8_t threshold)
{
    I2Cdev_writeByte(devAddr, MPU6050_RA_FF_THR, threshold);
}

// FF_DUR register

/** Get free-fall event duration threshold.
 * This register configures the duration counter threshold for Free Fall event
 * detection. The duration counter ticks at 1kHz, therefore FF_DUR has a unit
 * of 1 LSB = 1 ms.
 *
 * The Free Fall duration counter increments while the absolute value of the
 * accelerometer measurements are each less than the detection threshold
 * (Register 29). The Free Fall interrupt is triggered when the Free Fall
 * duration counter reaches the time specified in this register.
 *
 * For more details on the Free Fall detection interrupt, see Section 8.2 of
 * the MPU-6000/MPU-6050 Product Specification document as well as Registers 56
 * and 58 of this document.
 *
 * @return Current free-fall duration threshold value (LSB = 1ms)
 * @see MPU6050_RA_FF_DUR
 */
uint8_t MPU6050::getFreefallDetectionDuration()
{
    I2Cdev_readByte(devAddr, MPU6050_RA_FF_DUR, buffer);
    return buffer[0];
}

/** Get free-fall event duration threshold.
 * @param duration New free-fall duration threshold value (LSB = 1ms)
 * @see getFreefallDetectionDuration()
 * @see MPU6050_RA_FF_DUR
 */
void MPU6050::setFreefallDetectionDuration(uint8_t duration)
{
    I2Cdev_writeByte(devAddr, MPU6050_RA_FF_DUR, duration);
}

// MOT_THR register

/** Get motion detection event acceleration threshold.
 * This register configures the detection threshold for Motion interrupt
 * generation. The unit of MOT_THR is 1LSB = 2mg. Motion is detected when the
 * absolute value of any of the accelerometer measurements exceeds this Motion
 * detection threshold. This condition increments the Motion detection duration
 * counter (Register 32). The Motion detection interrupt is triggered when the
 * Motion Detection counter reaches the time count specified in MOT_DUR
 * (Register 32).
 *
 * The Motion interrupt will indicate the axis and polarity of detected motion
 * in MOT_DETECT_STATUS (Register 97).
 *
 * For more details on the Motion detection interrupt, see Section 8.3 of the
 * MPU-6000/MPU-6050 Product Specification document as well as Registers 56 and
 * 58 of this document.
 *
 * @return Current motion detection acceleration threshold value (LSB = 2mg)
 * @see MPU6050_RA_MOT_THR
 */
uint8_t MPU6050::getMotionDetectionThreshold()
{
    I2Cdev_readByte(devAddr, MPU6050_RA_MOT_THR, buffer);
    return buffer[0];
}

/** Set motion detection event acceleration threshold.
 * @param threshold New motion detection acceleration threshold value (LSB = 2mg)
 * @see getMotionDetectionThreshold()
 * @see MPU6050_RA_MOT_THR
 */
void MPU6050::setMotionDetectionThreshold(uint8_t threshold)
{
    I2Cdev_writeByte(devAddr, MPU6050_RA_MOT_THR, threshold);
}

// MOT_DUR register

/** Get motion detection event duration threshold.
 * This register configures the duration counter threshold for Motion interrupt
 * generation. The duration counter ticks at 1 kHz, therefore MOT_DUR has a unit
 * of 1LSB = 1ms. The Motion detection duration counter increments when the
 * absolute value of any of the accelerometer measurements exceeds the Motion
 * detection threshold (Register 31). The Motion detection interrupt is
 * triggered when the Motion detection counter reaches the time count specified
 * in this register.
 *
 * For more details on the Motion detection interrupt, see Section 8.3 of the
 * MPU-6000/MPU-6050 Product Specification document.
 *
 * @return Current motion detection duration threshold value (LSB = 1ms)
 * @see MPU6050_RA_MOT_DUR
 */
uint8_t MPU6050::getMotionDetectionDuration()
{
    I2Cdev_readByte(devAddr, MPU6050_RA_MOT_DUR, buffer);
    return buffer[0];
}

/** Set motion detection event duration threshold.
 * @param duration New motion detection duration threshold value (LSB = 1ms)
 * @see getMotionDetectionDuration()
 * @see MPU6050_RA_MOT_DUR
 */
void MPU6050::setMotionDetectionDuration(uint8_t duration)
{
    I2Cdev_writeByte(devAddr, MPU6050_RA_MOT_DUR, duration);
}

// ZRMOT_THR register

/** Get zero motion detection event acceleration threshold.
 * This register configures the detection threshold for Zero Motion interrupt
 * generation. The unit of ZRMOT_THR is 1LSB = 2mg. Zero Motion is detected when
 * the absolute value of the accelerometer measurements for the 3 axes are each
 * less than the detection threshold. This condition increments the Zero Motion
 * duration counter (Register 34). The Zero Motion interrupt is triggered when
 * the Zero Motion duration counter reaches the time count specified in
 * ZRMOT_DUR (Register 34).
 *
 * Unlike Free Fall or Motion detection, Zero Motion detection triggers an
 * interrupt both when Zero Motion is first detected and when Zero Motion is no
 * longer detected.
 *
 * When a zero motion event is detected, a Zero Motion Status will be indicated
 * in the MOT_DETECT_STATUS register (Register 97). When a motion-to-zero-motion
 * condition is detected, the status bit is set to 1. When a zero-motion-to-
 * motion condition is detected, the status bit is set to 0.
 *
 * For more details on the Zero Motion detection interrupt, see Section 8.4 of
 * the MPU-6000/MPU-6050 Product Specification document as well as Registers 56
 * and 58 of this document.
 *
 * @return Current zero motion detection acceleration threshold value (LSB = 2mg)
 * @see MPU6050_RA_ZRMOT_THR
 */
uint8_t MPU6050::getZeroMotionDetectionThreshold()
{
    I2Cdev_readByte(devAddr, MPU6050_RA_ZRMOT_THR, buffer);
    return buffer[0];
}

/** Set zero motion detection event acceleration threshold.
 * @param threshold New zero motion detection acceleration threshold value (LSB = 2mg)
 * @see getZeroMotionDetectionThreshold()
 * @see MPU6050_RA_ZRMOT_THR
 */
void MPU6050::setZeroMotionDetectionThreshold(uint8_t threshold)
{
    I2Cdev_writeByte(devAddr, MPU6050_RA_ZRMOT_THR, threshold);
}

// ZRMOT_DUR register

/** Get zero motion detection event duration threshold.
 * This register configures the duration counter threshold for Zero Motion
 * interrupt generation. The duration counter ticks at 16 Hz, therefore
 * ZRMOT_DUR has a unit of 1 LSB = 64 ms. The Zero Motion duration counter
 * increments while the absolute value of the accelerometer measurements are
 * each less than the detection threshold (Register 33). The Zero Motion
 * interrupt is triggered when the Zero Motion duration counter reaches the time
 * count specified in this register.
 *
 * For more details on the Zero Motion detection interrupt, see Section 8.4 of
 * the MPU-6000/MPU-6050 Product Specification document, as well as Registers 56
 * and 58 of this document.
 *
 * @return Current zero motion detection duration threshold value (LSB = 64ms)
 * @see MPU6050_RA_ZRMOT_DUR
 */
uint8_t MPU6050::getZeroMotionDetectionDuration()
{
    I2Cdev_readByte(devAddr, MPU6050_RA_ZRMOT_DUR, buffer);
    return buffer[0];
}

/** Set zero motion detection event duration threshold.
 * @param duration New zero motion detection duration threshold value (LSB = 1ms)
 * @see getZeroMotionDetectionDuration()
 * @see MPU6050_RA_ZRMOT_DUR
 */
void MPU6050::setZeroMotionDetectionDuration(uint8_t duration)
{
    I2Cdev_writeByte(devAddr, MPU6050_RA_ZRMOT_DUR, duration);
}

// FIFO_EN register

/** Get temperature FIFO enabled value.
 * When set to 1, this bit enables TEMP_OUT_H and TEMP_OUT_L (Registers 65 and
 * 66) to be written into the FIFO buffer.
 * @return Current temperature FIFO enabled value
 * @see MPU6050_RA_FIFO_EN
 */
bool MPU6050::getTempFIFOEnabled()
{
    I2Cdev_readBit(devAddr, MPU6050_RA_FIFO_EN, MPU6050_TEMP_FIFO_EN_BIT, buffer);
    return buffer[0];
}

/** Set temperature FIFO enabled value.
 * @param enabled New temperature FIFO enabled value
 * @see getTempFIFOEnabled()
 * @see MPU6050_RA_FIFO_EN
 */
void MPU6050::setTempFIFOEnabled(bool enabled)
{
    I2Cdev_writeBit(devAddr, MPU6050_RA_FIFO_EN, MPU6050_TEMP_FIFO_EN_BIT, enabled);
}

/** Get gyroscope X-axis FIFO enabled value.
 * When set to 1, this bit enables GYRO_XOUT_H and GYRO_XOUT_L (Registers 67 and
 * 68) to be written into the FIFO buffer.
 * @return Current gyroscope X-axis FIFO enabled value
 * @see MPU6050_RA_FIFO_EN
 */
bool MPU6050::getXGyroFIFOEnabled()
{
    I2Cdev_readBit(devAddr, MPU6050_RA_FIFO_EN, MPU6050_XG_FIFO_EN_BIT, buffer);
    return buffer[0];
}

/** Set gyroscope X-axis FIFO enabled value.
 * @param enabled New gyroscope X-axis FIFO enabled value
 * @see getXGyroFIFOEnabled()
 * @see MPU6050_RA_FIFO_EN
 */
void MPU6050::setXGyroFIFOEnabled(bool enabled)
{
    I2Cdev_writeBit(devAddr, MPU6050_RA_FIFO_EN, MPU6050_XG_FIFO_EN_BIT, enabled);
}

/** Get gyroscope Y-axis FIFO enabled value.
 * When set to 1, this bit enables GYRO_YOUT_H and GYRO_YOUT_L (Registers 69 and
 * 70) to be written into the FIFO buffer.
 * @return Current gyroscope Y-axis FIFO enabled value
 * @see MPU6050_RA_FIFO_EN
 */
bool MPU6050::getYGyroFIFOEnabled()
{
    I2Cdev_readBit(devAddr, MPU6050_RA_FIFO_EN, MPU6050_YG_FIFO_EN_BIT, buffer);
    return buffer[0];
}

/** Set gyroscope Y-axis FIFO enabled value.
 * @param enabled New gyroscope Y-axis FIFO enabled value
 * @see getYGyroFIFOEnabled()
 * @see MPU6050_RA_FIFO_EN
 */
void MPU6050::setYGyroFIFOEnabled(bool enabled)
{
    I2Cdev_writeBit(devAddr, MPU6050_RA_FIFO_EN, MPU6050_YG_FIFO_EN_BIT, enabled);
}
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
